markusbackman/lovglod/src/settings.cpp

#include "settings.h"
#include <Preferences.h>
#include "config.h"

Settings settings;
static Preferences prefs;
static const char *NS = "lovenled";

void Settings::load() {
    prefs.begin(NS, /*readOnly=*/true);
    wifiSsid        = prefs.getString("ssid", "");
    wifiPass        = prefs.getString("pass", "");
    otaSource       = prefs.getString("otasrc", OTA_DEFAULT_SOURCE);
    otaBeta         = prefs.getBool("otabeta", false);
    otaBadVersion   = prefs.getString("otabadv", "");
    otaPendingVersion = prefs.getString("otapend", "");
    otaBadCount     = prefs.getUChar("otabadc", 0);
    brightness      = prefs.getUChar("bright", LED_DEFAULT_BRIGHTNESS);
    debugPush       = prefs.getBool("dbgpush", false);
    goalDelayS      = prefs.getUChar("goaldly", GOAL_DELAY_DEFAULT_S);
    lampMode        = (LampMode)prefs.getUChar("lampmode", LAMP_ALWAYS);
    matchLeadMin    = prefs.getUChar("leadmin", MATCH_LEAD_DEFAULT_MIN);
    victoryUntil    = prefs.getULong("victuntil", 0);
    victoryGame     = prefs.getULong("victgame", 0);
    ledStrip        = (LedStrip)prefs.getUChar("ledstrip", LED_STRIP_UNSET);
    ledCount        = prefs.getUShort("ledcount", LED_COUNT_DEFAULT);
    liveUuid        = prefs.getString("liveuuid", "");
    liveStart       = prefs.getULong("livestart", 0);
    liveHome        = prefs.getString("livehome", "");
    liveAway        = prefs.getString("liveaway", "");
    liveScoreHome   = prefs.getChar("livesh", -1);
    liveScoreAway   = prefs.getChar("livesa", -1);
    bootCount       = prefs.getULong("boots", 0);
    abnormalBoots   = prefs.getULong("badboots", 0);
    telemetry       = prefs.getBool("tele", true);
    lampId          = prefs.getString("lampid", "");
    lampName        = prefs.getString("lampname", "");

    // Lampor från före listvalet har WiFi men ingen listnyckel. De sitter alla
    // med WS2812B — det var den enda list firmwaren kunde driva — och utan det
    // här skulle varje lampa ute i fält börja driva båda utgångarna efter OTA.
    const bool legacy = !prefs.isKey("ledstrip") && wifiSsid.length();
    prefs.end();

    if (goalDelayS > GOAL_DELAY_MAX_S) goalDelayS = GOAL_DELAY_MAX_S;
    if (ledStrip > LED_STRIP_APA102)   ledStrip = LED_STRIP_UNSET;
    if (lampMode > LAMP_OFF)           lampMode = LAMP_ALWAYS;
    if (!matchLeadMin)                 matchLeadMin = MATCH_LEAD_DEFAULT_MIN;
    ledCount = constrain(ledCount, LED_COUNT_MIN, LED_COUNT_MAX);

    // Slumpas en gång och sparas direkt. esp_random() är en riktig
    // slumpkälla när radion är igång, men redan här räcker den gott för att
    // tre lampor inte ska få samma ID.
    const bool newId = lampId.length() != 16;
    if (newId) {
        char buf[17];
        snprintf(buf, sizeof(buf), "%08lx%08lx",
                 (unsigned long)esp_random(), (unsigned long)esp_random());
        lampId = buf;
    }

    if (legacy) ledStrip = LED_STRIP_WS2812;
    if (legacy || newId) save();
}

void Settings::save() {
    prefs.begin(NS, /*readOnly=*/false);
    prefs.putString("ssid", wifiSsid);
    prefs.putString("pass", wifiPass);
    prefs.putString("otasrc", otaSource);
    prefs.putBool("otabeta", otaBeta);
    prefs.putString("otabadv", otaBadVersion);
    prefs.putString("otapend", otaPendingVersion);
    prefs.putUChar("otabadc", otaBadCount);
    prefs.putUChar("bright", brightness);
    prefs.putBool("dbgpush", debugPush);
    prefs.putUChar("goaldly", goalDelayS);
    prefs.putUChar("lampmode", lampMode);
    prefs.putUChar("leadmin", matchLeadMin);
    prefs.putULong("victuntil", victoryUntil);
    prefs.putULong("victgame", victoryGame);
    prefs.putUChar("ledstrip", ledStrip);
    prefs.putUShort("ledcount", ledCount);
    prefs.putBool("tele", telemetry);
    prefs.putString("lampid", lampId);
    prefs.putString("lampname", lampName);
    prefs.end();
}

// Skriver bara räknarna, inte hela inställningsblocket — det här körs vid varje
// start, även i en omstartsloop.
void Settings::noteBoot(bool poweredOn, bool abnormal) {
    bootCount++;
    if (poweredOn)     abnormalBoots = 0;
    else if (abnormal) abnormalBoots++;

    prefs.begin(NS, /*readOnly=*/false);
    prefs.putULong("boots", bootCount);
    prefs.putULong("badboots", abnormalBoots);
    prefs.end();
}

// Egen skrivning, som noteBoot(): matchen sparas mitt i drift och ska inte
// dra med sig resten av inställningarna.
void Settings::noteLiveGame(const String &uuid, uint32_t startUtc,
                            const String &home, const String &away) {
    if (uuid == liveUuid && startUtc == liveStart) return;
    liveUuid = uuid; liveStart = startUtc; liveHome = home; liveAway = away;
    liveScoreHome = liveScoreAway = -1;
    prefs.begin(NS, /*readOnly=*/false);
    prefs.putChar("livesh", -1);
    prefs.putChar("livesa", -1);
    prefs.putString("liveuuid", liveUuid);
    prefs.putULong("livestart", liveStart);
    prefs.putString("livehome", liveHome);
    prefs.putString("liveaway", liveAway);
    prefs.end();
}

void Settings::noteLiveScore(int home, int away) {
    if (home == liveScoreHome && away == liveScoreAway) return;
    liveScoreHome = home; liveScoreAway = away;
    prefs.begin(NS, /*readOnly=*/false);
    prefs.putChar("livesh", liveScoreHome);
    prefs.putChar("livesa", liveScoreAway);
    prefs.end();
}

void Settings::clearWifi() {
    wifiSsid = "";
    wifiPass = "";
    save();
}

void Settings::noteVictory(uint32_t gameStartUtc, uint32_t untilUtc) {
    victoryGame  = gameStartUtc;
    victoryUntil = untilUtc;
    save();
}

// Nollar bara sluttiden. victoryGame ligger kvar — den är kvittot på att
// matchen redan är firad, och utan den skulle nästa hämtning tända om läget.
void Settings::clearVictory() {
    if (!victoryUntil) return;
    victoryUntil = 0;
    save();
}

// Räkna upp misslyckanden för en specifik version. Byter versionen börjar
// räknaren om — en ny release ska alltid få ett ärligt försök.
void Settings::noteOtaFailure(const String &version) {
    if (otaBadVersion != version) {
        otaBadVersion = version;
        otaBadCount   = 0;
    }
    if (otaBadCount < 255) otaBadCount++;
    save();
}

// En version som installerades, startade och sedan rullades tillbaka har haft
// sin chans. Till skillnad från en misslyckad nedladdning — som gärna får
// försökas om — blockeras den direkt: den är bevisligen oanvändbar på just den
// här enheten, och varje nytt försök kostar 1 MB och två omstarter.
void Settings::noteOtaRollback(const String &version) {
    otaBadVersion     = version;
    otaBadCount       = OTA_MAX_FAILURES;
    otaPendingVersion = "";
    save();
}

void Settings::noteOtaPending(const String &version) {
    otaPendingVersion = version;
    save();
}

void Settings::clearOtaPending() {
    if (!otaPendingVersion.length()) return;
    otaPendingVersion = "";
    save();
}

void Settings::clearOtaFailures() {
    if (!otaBadVersion.length() && !otaBadCount) return;
    otaBadVersion = "";
    otaBadCount   = 0;
    save();
}

bool Settings::otaBlocked(const String &version) const {
    return otaBadVersion == version && otaBadCount >= OTA_MAX_FAILURES;
}
