markusbackman/lovglod/include/logo_svg.h

#pragma once
#include <Arduino.h>

// LövGlöds egen logotyp: ordmärket (Löv i vitt, Glöd i guld, guldstapel under)
// och kvadratmärket för fliken. Texten är konturer, så portalen behöver inget
// typsnitt — den har ändå inget internet att hämta ett från.
//
// IF Björklövens klubbmärke satt här förut. Det tillhör klubben, och lampan
// bär det redan i plasten; portalen använder produktens eget märke.

// Ordmärket, för den mörkgröna listen högst upp. Serveras som /logo.svg.
const char LOGO_SVG[] PROGMEM = R"SVG(<svg xmlns="http://www.w3.org/2000/svg" viewBox="-12 -115.80859375 338.453125 149.80859375" width="338" height="150" role="img" aria-label="LövGlöd">
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
<rect x="12" y="54" width="40" height="4" fill="#f8d12b"/>
</svg>)SVG";
