markusbackman/lovglod/src/shl.h

#pragma once
#include <Arduino.h>
#include <ArduinoJson.h>

struct NextGame {
    bool    valid    = false;
    String  uuid;
    String  homeCode;
    String  awayCode;
    time_t  startUtc = 0;      // nedsläpp, UTC epoch
    bool    homeIsUs = false;
};

struct LiveScore {
    bool valid = false;
    int  home  = -1;
    int  away  = -1;
};

// Senast spelade matchen. Att den alls dyker upp i played-games betyder att den
// är slut — SHL har ingen "matchen tog slut"-händelse, och matchfönstret i
// main.cpp är bara en timer på fyra timmar efter nedsläpp.
struct LastResult {
    bool   valid        = false;
    bool   won          = false;   // Björklöven vann (gnistorna, se main.cpp)
    time_t startUtc     = 0;       // nedsläpp, används som matchens identitet
    String summary;
};

// Matchläget ur live-strömmen, utöver ställningen. Allt är det senast
// rapporterade — lampan gissar aldrig framåt. Se "Matchljus" i config.h för
// hur ofta och hur sent det kommer.
enum class GameState : uint8_t { Unknown, Ongoing, Intermission, Overtime, Shootout, Decided };

struct LiveInfo {
    GameState state     = GameState::Unknown;
    GameState prevState = GameState::Unknown;
    uint32_t  stateRxMs = 0;       // millis() när state kom
    uint8_t   period    = 0;       // 1–3, 4 = övertid, 5 = straffar
    uint16_t  elapsedS  = 0;       // speltid i perioden enligt senaste klockramen
    bool      hasClock  = false;
};

namespace Shl {

// ── Pollning (HTTPS GET mot www.shl.se) ────────────────────────────────────
// Nästa match i spelschemat. Returnerar false vid nätverks-/parsfel.
bool fetchNextGame(NextGame &out);

// Senast spelade matchen. Returnerar false vid nätverks-/parsfel.
bool fetchLastResult(LastResult &out);

// Matchen som pågår just nu, från klubbsajten. En match som startat finns
// varken i upcoming-games eller played-games, så det här är enda vägen för en
// lampa som startar mitt i en match. Returnerar false när ingen match pågår,
// utan att sätta lastError() — det är inget fel.
bool fetchOngoingGame(NextGame &out);

// Reservväg under pågående match om SSE-strömmen inte ger något.
bool pollLiveScore(const String &gameUuid, LiveScore &out);

// ── Live-ström (Server-Sent Events mot game-broadcaster.s8y.se) ────────────
void sseStart(const String &gameUuid, time_t startUtc);
void sseStop();
bool sseConnected();

// Anropas varje varv i loop(). Returnerar true när en ny ställning lästs in.
bool ssePump(LiveScore &out);

// Matchläget enligt strömmen. Nollställs när strömmen startas för en ny match.
const LiveInfo &liveInfo();

// En ram utifrån, i samma format som strömmen, genom samma tolkning som
// strömmens ramar: liveState, gameTime och skott. Sant om ramen bar en
// ställning. För uppspelning av inspelade matcher via POST /push.
bool injectFrame(JsonVariantConst frame, LiveScore &out);

// Nollställer matchläget och skotten, som när strömmen startar för en ny match.
void resetLive();

// Skottryck just nu: skott per minut (båda lagen, avklingande) och balansen
// mellan lagen, -1–1 där +1 är att bara Björklöven skjuter.
void shotPressure(float &perMin, float &balance);

// ── Datakälla ──────────────────────────────────────────────────────────────
// Bas-URL:erna lampan hämtar från. Visas på felsökningssidan.
String apiBaseUrl();
String liveBaseUrl();

// ── Felsökning ─────────────────────────────────────────────────────────────
// Senaste råa SSE-ramen (kapad). Visas på enhetens /debug-sida så att
// fältformatet kan verifieras när säsongen väl drar igång.
const String &lastRawFrame();
const String &lastError();

// Räknare för diagnostikloggen.
uint32_t sseFrames();
uint32_t sseReconnects();
uint32_t httpErrors();      // misslyckade GET mot SHL sedan start
uint32_t sseComments();
uint32_t sseSilentMs();

}  // namespace Shl
