markusbackman/lovglod/include/ota_pubkey.h

#pragma once

// Publik nyckel för OTA-signaturkontroll. Genererad av
// tools/generate-ota-key.sh — redigera inte för hand.
//
// Den här filen SKA ligga i repot. En publik nyckel är publik; det är den
// privata motsvarigheten (ota_signing_key.pem, .gitignore:ad och lagrad som
// GitHub-secret OTA_SIGNING_KEY) som är hemligheten.
//
// Enheten vägrar installera firmware som inte är signerad med motsvarande
// privata nyckel. Saknas eller går nyckeln inte att tolka stängs self-update
// av helt — den faller aldrig tillbaka på att installera osignerat.
//
// Array och inte #define: ett makro slutar vid radslutet, så ett flerradigt
// raw-string-literal går inte att stoppa in i ett. Headern inkluderas bara av
// updater.cpp, så den interna länkningen kostar ingenting.
static const char OTA_PUBLIC_KEY_PEM[] = R"PEM(
-----BEGIN PUBLIC KEY-----
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
XQIDAQAB
-----END PUBLIC KEY-----
)PEM";
